YePererva/ST-Link-v2.1-mini/references/10-pin SWD/10pin_-_Copy.jpg

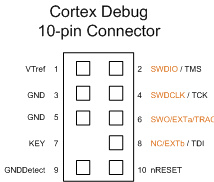
references/10-pin SWD/10pin_-_Copy.jpg
