YePererva/ST-Link-v2.1-mini/references/JTAG/ulinkme2_connector_20_10_pin_jtag.png

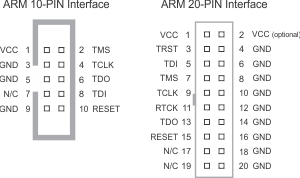
references/JTAG/ulinkme2_connector_20_10_pin_jtag.png
