YePererva/ST-Link-v2.1-mini/references/project-of-other/bottom.jpg

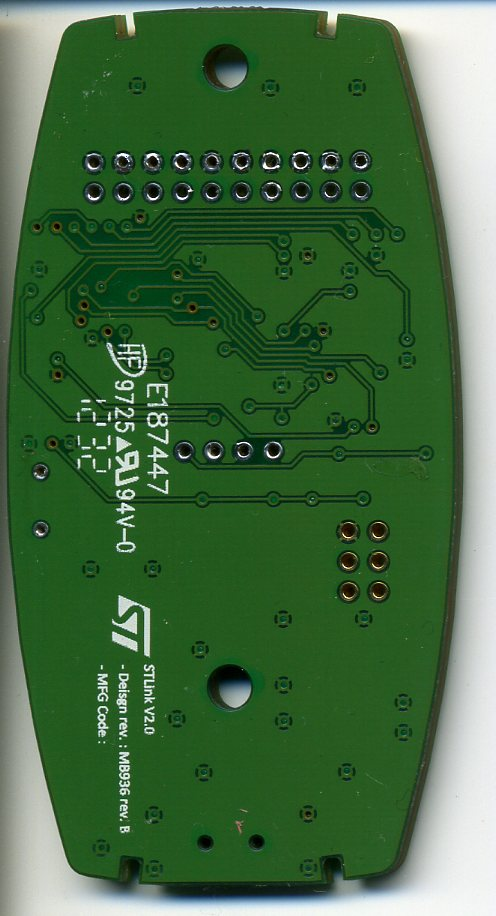
references/project-of-other/bottom.jpg
