YePererva/ST-Link-v2.1-mini/references/st-link made by others/isolated/STLinkV2-1_ISOL.jpg

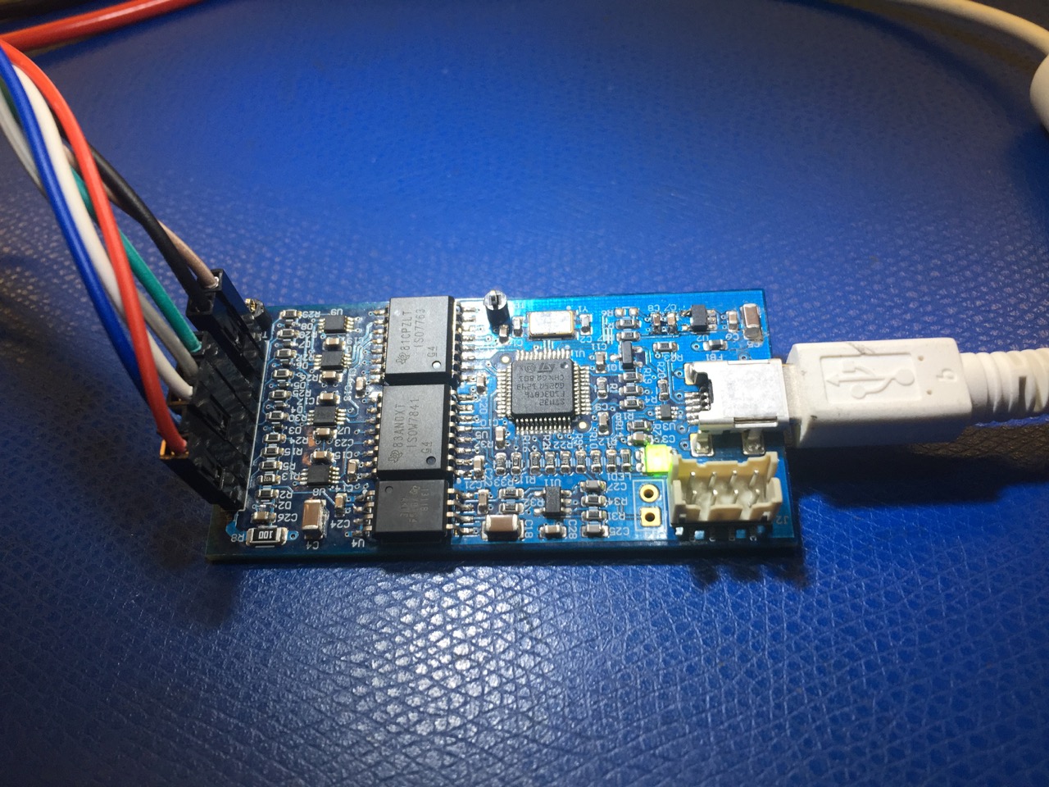
references/st-link made by others/isolated/STLinkV2-1_ISOL.jpg
