YePererva/ST-Link-v2.1-mini/references/st-link made by others/shemf_st_link_v2.jpg

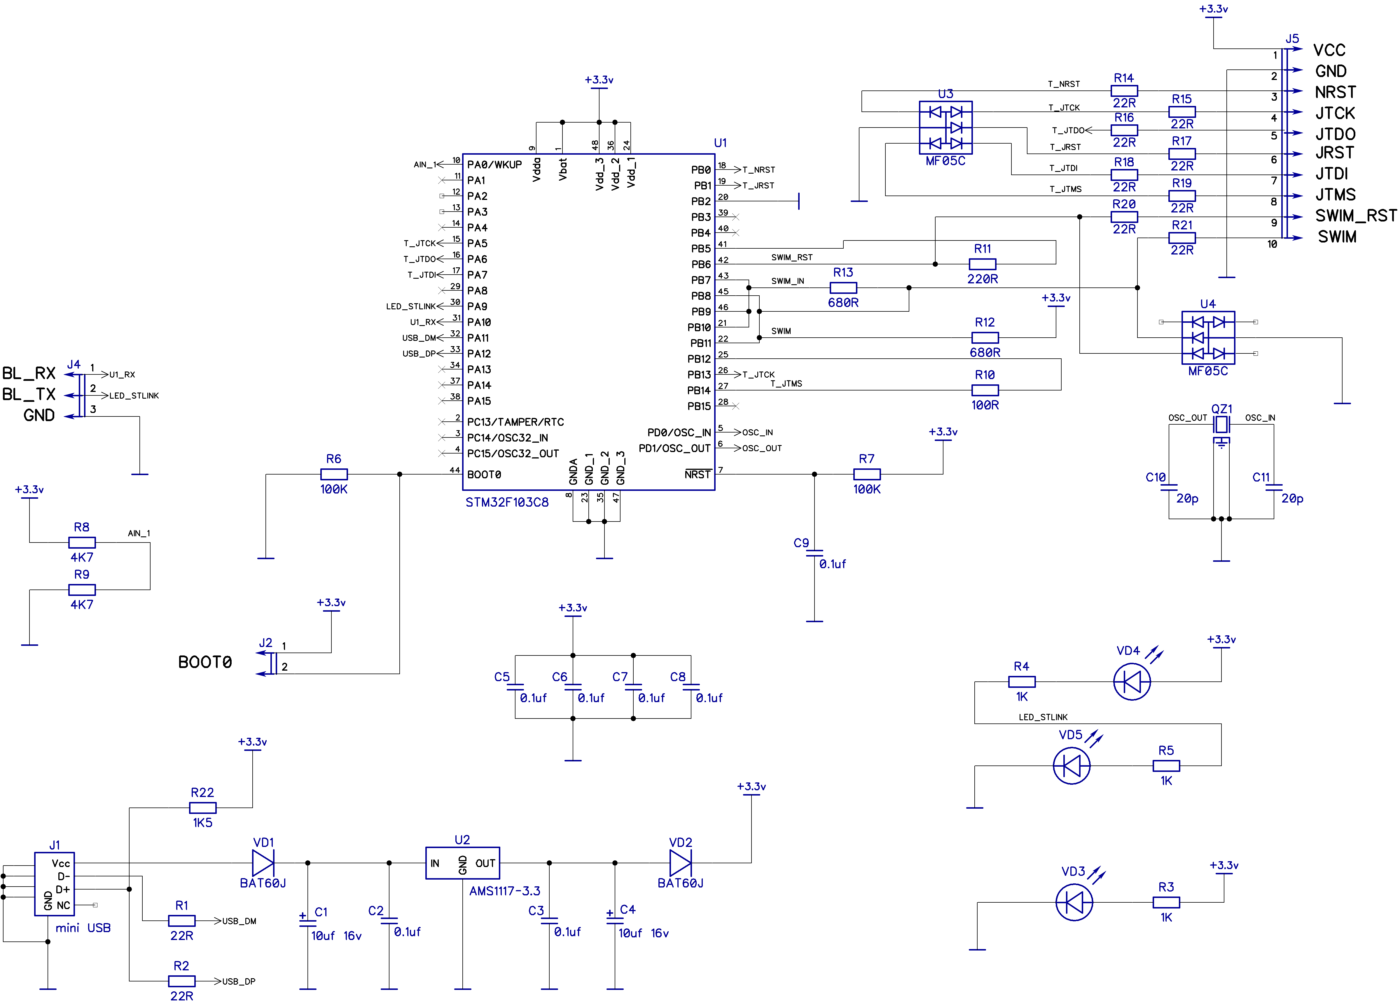
references/st-link made by others/shemf_st_link_v2.jpg
