YePererva/ST-Link-v2.1-mini/references/st-link made by others/st-link_isolated.jpg

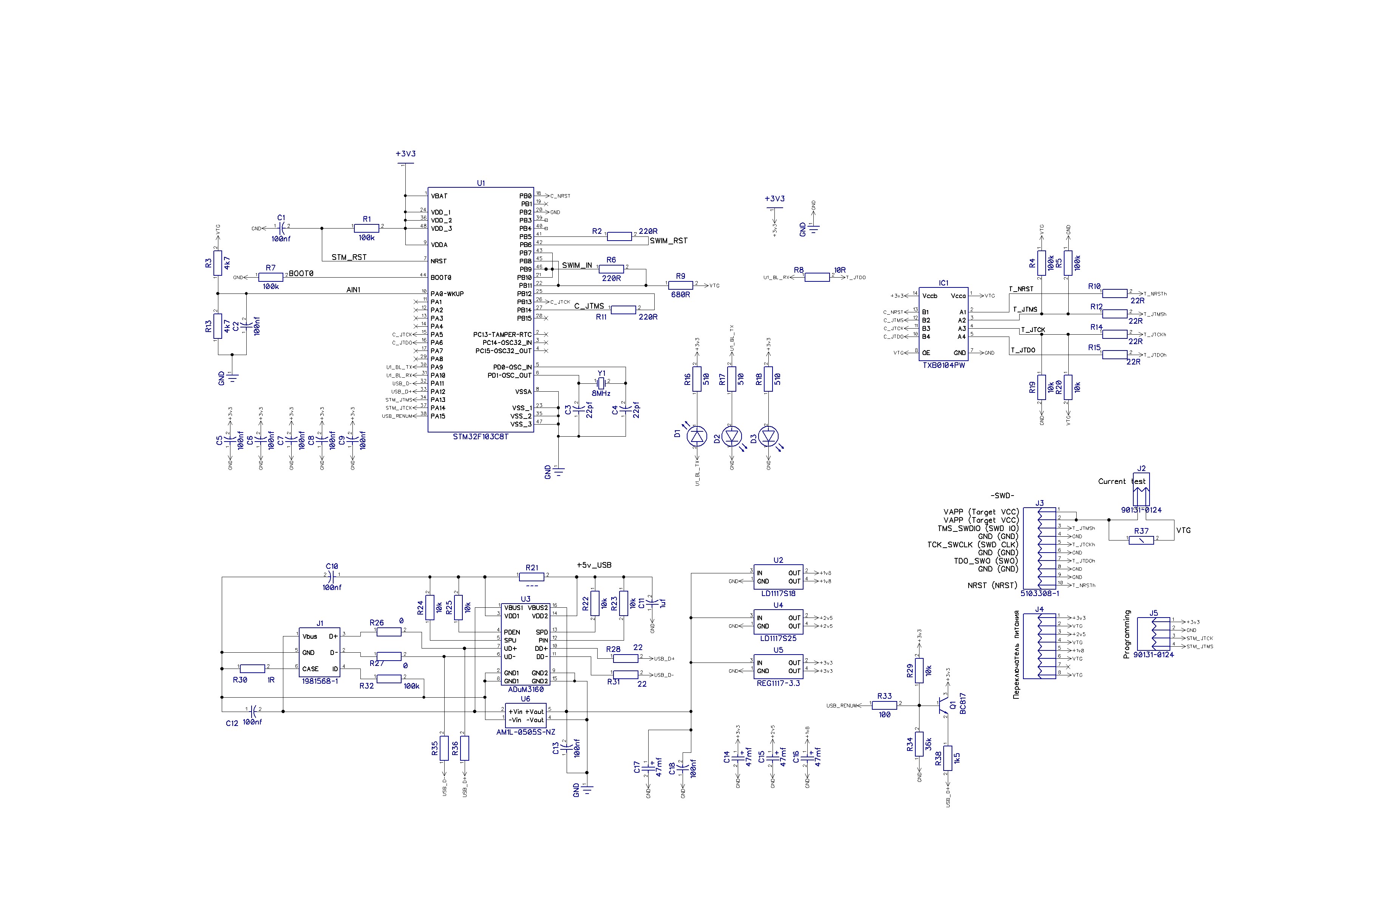
references/st-link made by others/st-link_isolated.jpg
