YePererva/ST-Link-v2.1-mini/references/st-link made by others/П_stlink_html_178dc41a294fdc49.png

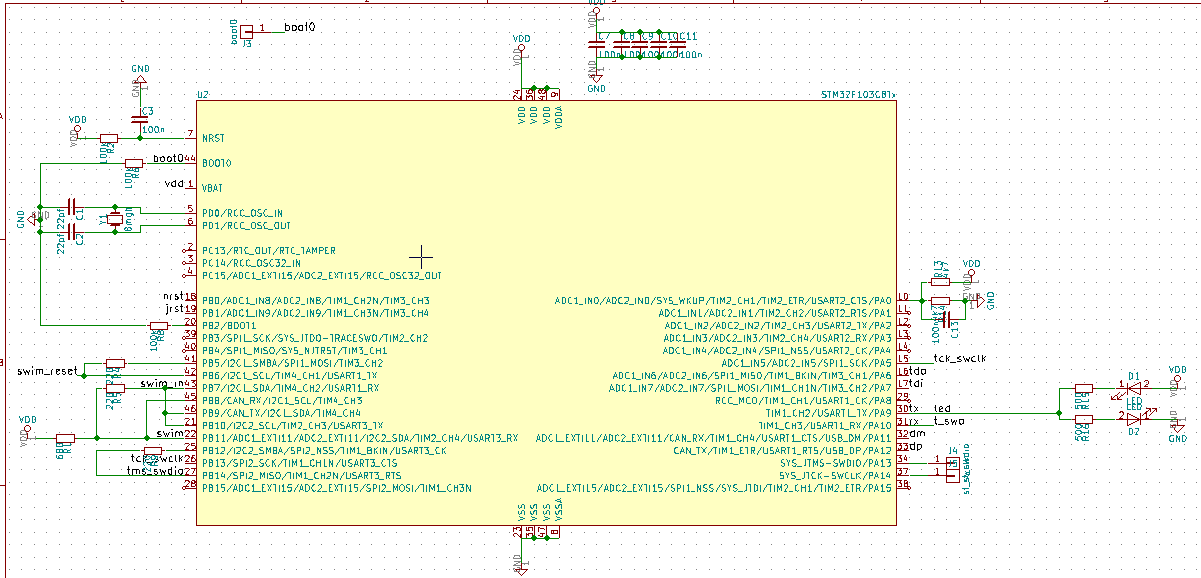
references/st-link made by others/П_stlink_html_178dc41a294fdc49.png
