YePererva/ST-Link-v2.1-mini/references/st-link made by others/П_stlink_html_f65d1a81e4980048.jpg

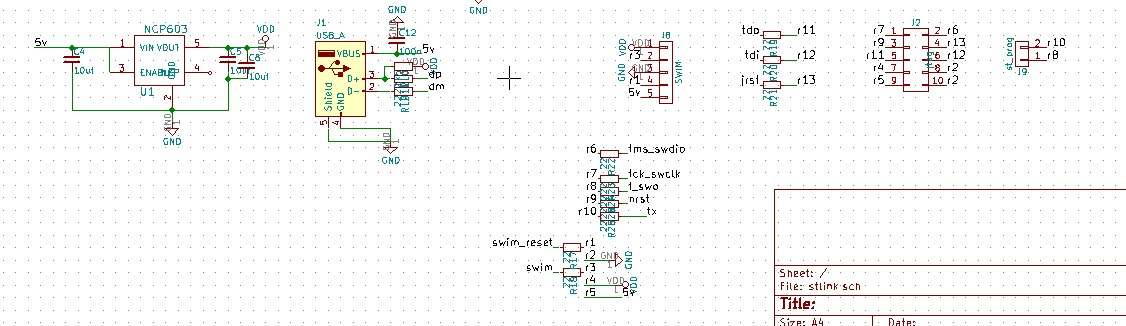
references/st-link made by others/П_stlink_html_f65d1a81e4980048.jpg
