YePererva/ST-Link-v2.1-mini/references/STDC14/on the target.png

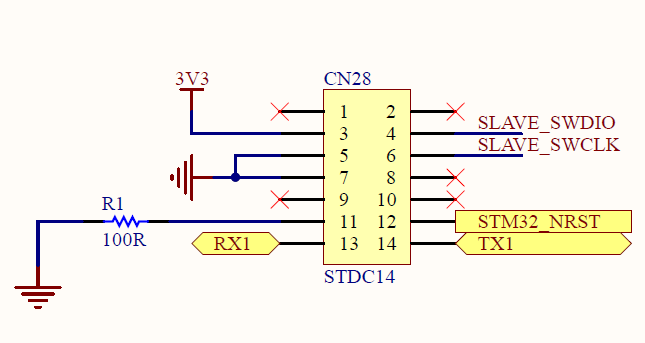
references/STDC14/on the target.png
