YePererva/ST-Link-v2.1-mini/references/SWIM/2019-09-25_14-02-29.png

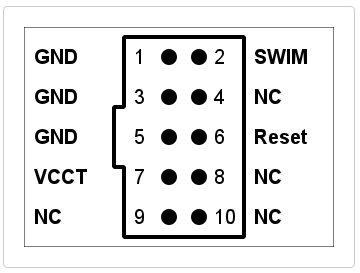
references/SWIM/2019-09-25_14-02-29.png
