YePererva/ST-Link-v2.1-mini/references/SWIM/2019-09-25_14-06-57.webp

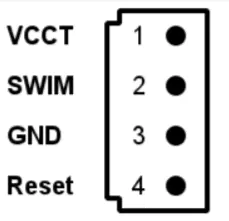
references/SWIM/2019-09-25_14-06-57.webp
