YePererva/ST-Link-v2.1-mini/references/SWIM/2019-09-25_14-07-37.webp

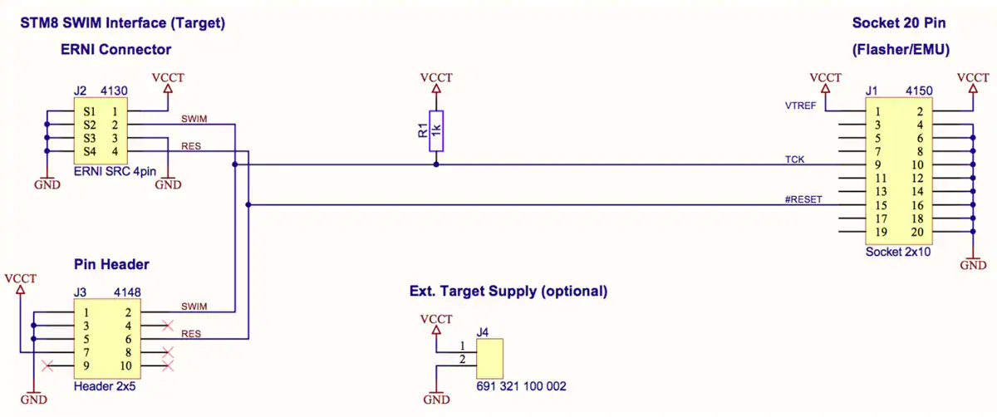
references/SWIM/2019-09-25_14-07-37.webp
